obbo-pl/RC-RX-NRF24L01/firmware/RSSI.cpp

/*
 Copyright 2017 by Dennis Cabell
 KE8FZX
 
 To use this software, you must adhere to the license terms described below, and assume all responsibility for the use
 of the software.  The user is responsible for all consequences or damage that may result from using this software.
 The user is responsible for ensuring that the hardware used to run this software complies with local regulations and that 
 any radio signal generated from use of this software is legal for that user to generate.  The author(s) of this software 
 assume no liability whatsoever.  The author(s) of this software is not responsible for legal or civil consequences of 
 using this software, including, but not limited to, any damages cause by lost control of a vehicle using this software.  
 If this software is copied or modified, this disclaimer must accompany all copies.
 
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
 You should have received a copy of the GNU General Public License
 along with RC_RX_CABELL_V3_FHSS.  If not, see <http://www.gnu.org/licenses/>.
 */

#include "RSSI.h" 
#define constrain(amt,low,high) ((amt)<(low)?(low):((amt)>(high)?(high):(amt)))
                        
//--------------------------------------------------------------------------------------------------------------------------
RSSI::RSSI ()
{
	resetCounters();
    packetRate = 0;
    sequentialMissTrack = 0;
}

//--------------------------------------------------------------------------------------------------------------------------
void RSSI::hit() {
  hitCount++;
  sequentialMissTrack = constrain(sequentialMissTrack - RSSI_MISS_ADJUSTMENT_RECOVERY,TELEMETRY_RSSI_MIN_VALUE,TELEMETRY_RSSI_MAX_VALUE);
  packetProcess();
}

//--------------------------------------------------------------------------------------------------------------------------
void RSSI::miss() {
  missCount++;
  sequentialMissTrack = constrain(sequentialMissTrack + RSSI_MISS_ADJUSTMENT,TELEMETRY_RSSI_MIN_VALUE,TELEMETRY_RSSI_MAX_VALUE);
  packetProcess();
}

//--------------------------------------------------------------------------------------------------------------------------
void RSSI::secondaryHit() {
  secondaryHitCount++;
}

//--------------------------------------------------------------------------------------------------------------------------
void RSSI::badPacket() {
  // bad packets generally don't happen, but it will also count as a hit since the error was likely introduced on the SPI bus since it passed the NRF24L01 internal checksum
  badPacketCount++;
  hit();
}

//--------------------------------------------------------------------------------------------------------------------------
void RSSI::packetProcess() {
  packetCount++;
  if (packetCount >= RSSI_CALC_INTERVAL) {
    packetRate = constrain((int)((float)(hitCount - badPacketCount) * 100.0 / (float)(hitCount + missCount)),TELEMETRY_RSSI_MIN_VALUE,TELEMETRY_RSSI_MAX_VALUE);
    resetCounters();
  }
}

//--------------------------------------------------------------------------------------------------------------------------
void RSSI::resetCounters() {
  hitCount = 0;
  missCount = 0;
  secondaryHitCount = 0;
  badPacketCount = 0;
  packetCount = 0;
}

//--------------------------------------------------------------------------------------------------------------------------
uint8_t RSSI::getRSSI() {
 return constrain(packetRate - sequentialMissTrack,TELEMETRY_RSSI_MIN_VALUE,TELEMETRY_RSSI_MAX_VALUE);
}
